Neil427/PEGASUS_2023_REVIVAL/Images/AamberPegasus6809.jpeg

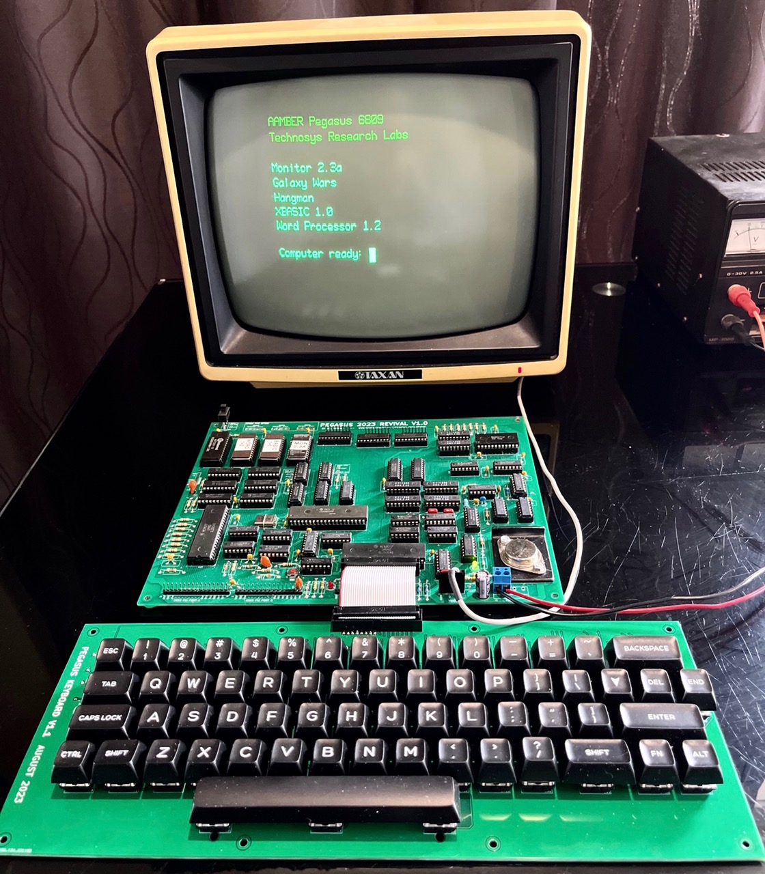
Images/AamberPegasus6809.jpeg
