Neil427/PEGASUS_2023_REVIVAL/Images/AamberPegasus6809b.jpeg

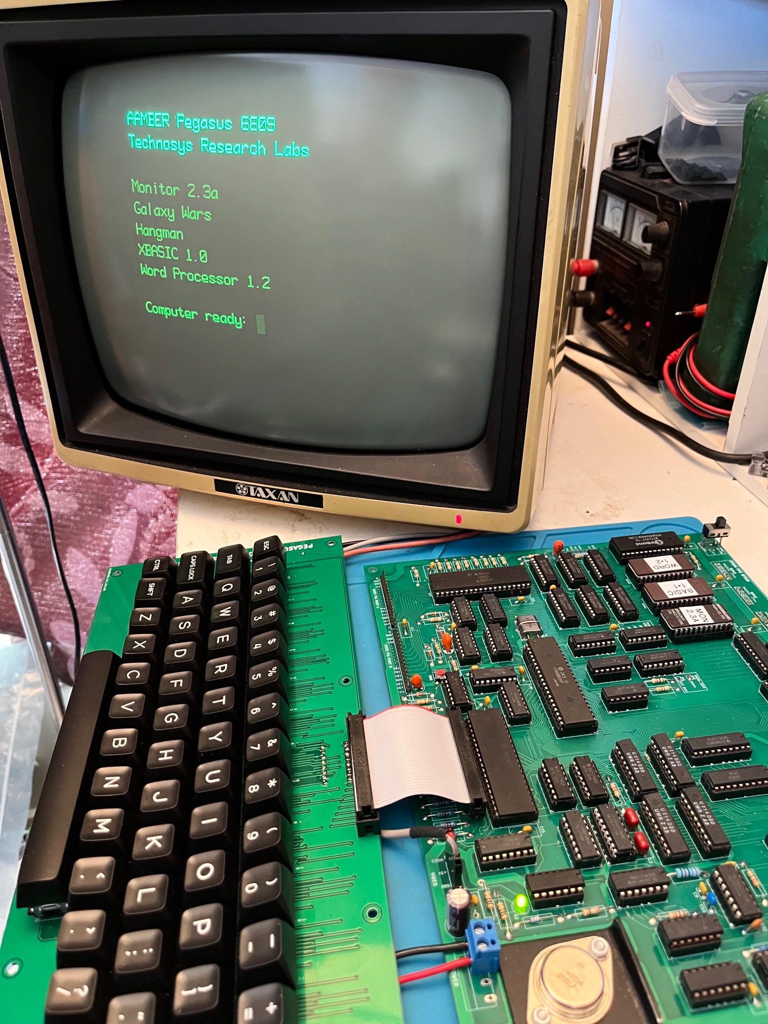
Images/AamberPegasus6809b.jpeg
