Neil427/PEGASUS_2023_REVIVAL/Images/OriginalPCBbottom.png

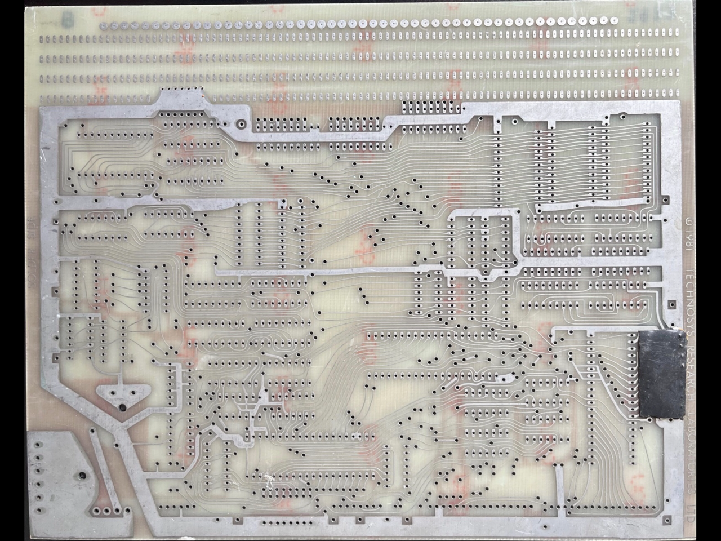
Images/OriginalPCBbottom.png
