Neil427/PEGASUS_2023_REVIVAL/Images/Pegasus The First Powerup.jpeg

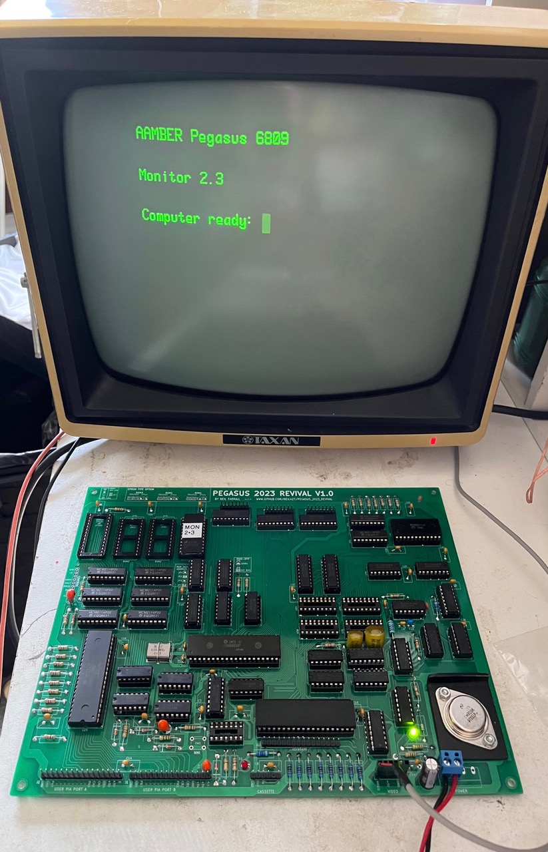
Images/Pegasus The First Powerup.jpeg
