Neil427/PEGASUS_2023_REVIVAL/Images/PegasusGalaxywars.jpeg

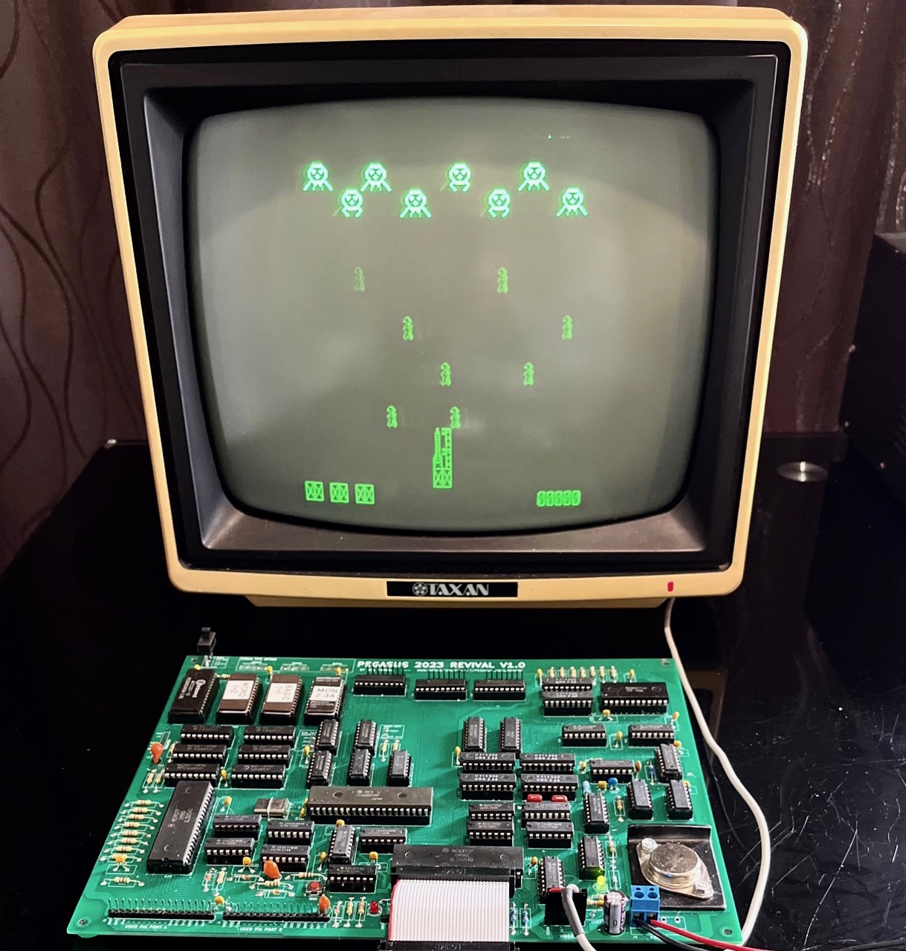
Images/PegasusGalaxywars.jpeg
