Neil427/PEGASUS_2023_REVIVAL/Images/PegasusHangman3.jpeg

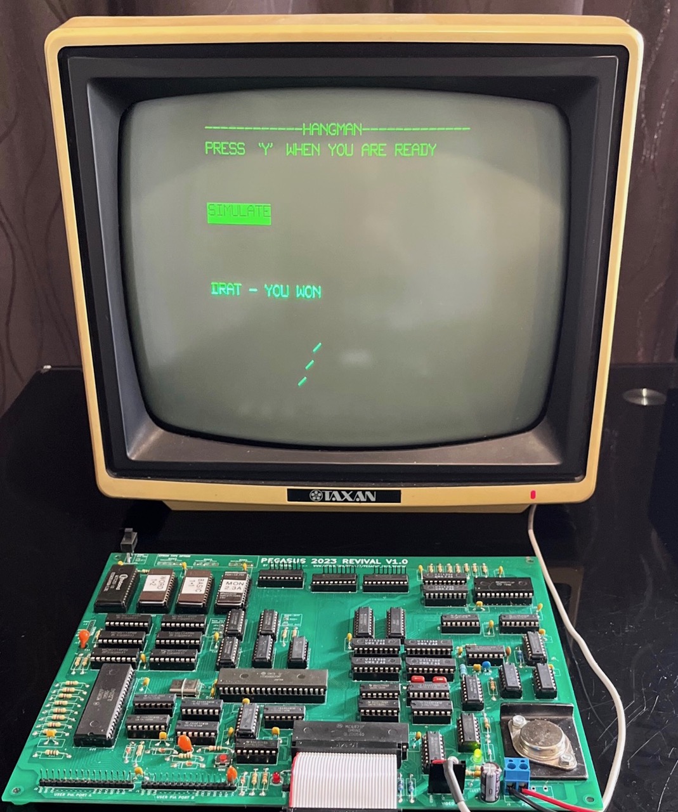
Images/PegasusHangman3.jpeg
