Neil427/PEGASUS_2023_REVIVAL/Images/PegasusHangman.jpeg

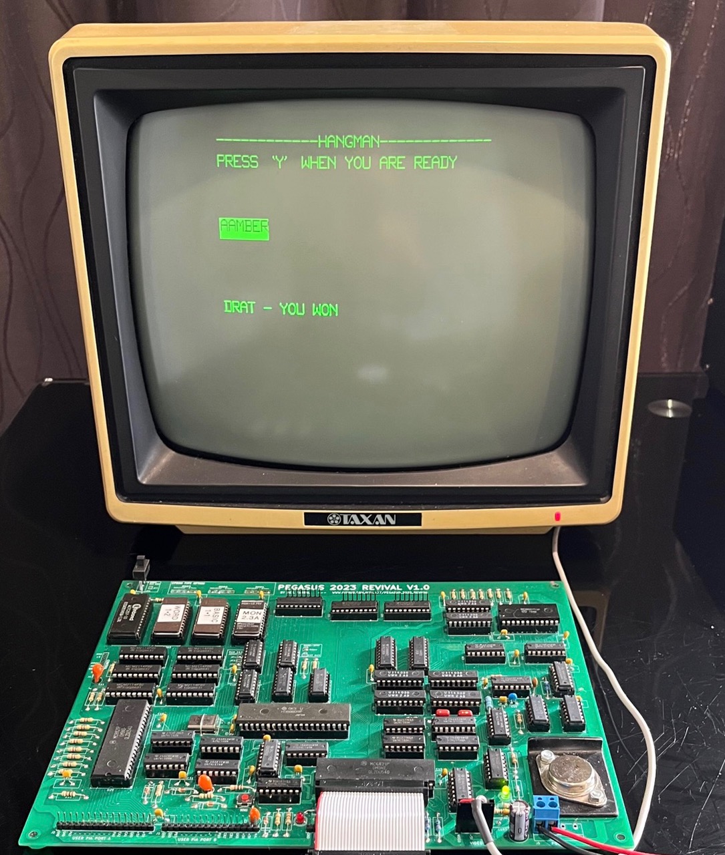
Images/PegasusHangman.jpeg
