Neil427/PEGASUS_2023_REVIVAL/Images/PegasusKeyboard.jpeg

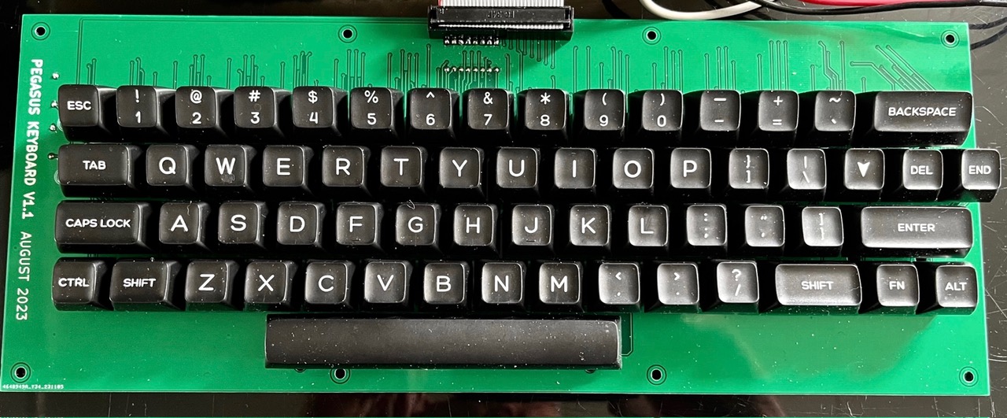
Images/PegasusKeyboard.jpeg
