Neil427/PEGASUS_2023_REVIVAL/Images/PegasusMainboard.jpeg

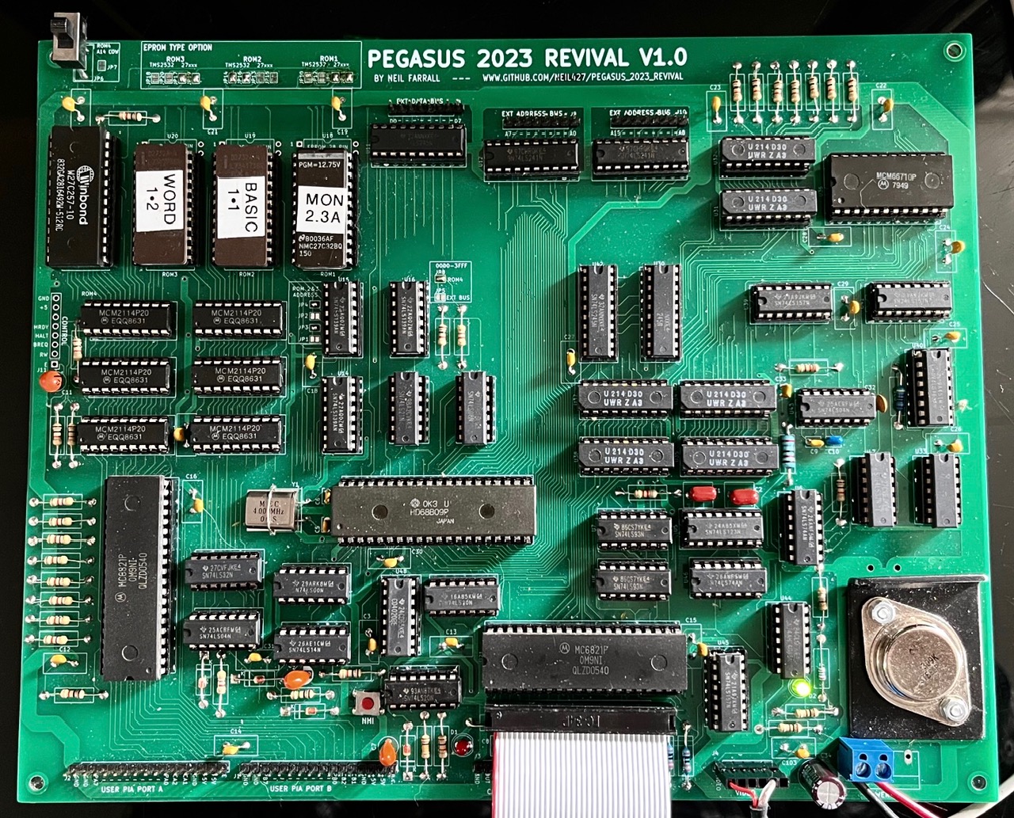
Images/PegasusMainboard.jpeg
