Neil427/PEGASUS_2023_REVIVAL/Keyboard_AamberPegasus2023Revival/Keyboard Keycaps.png

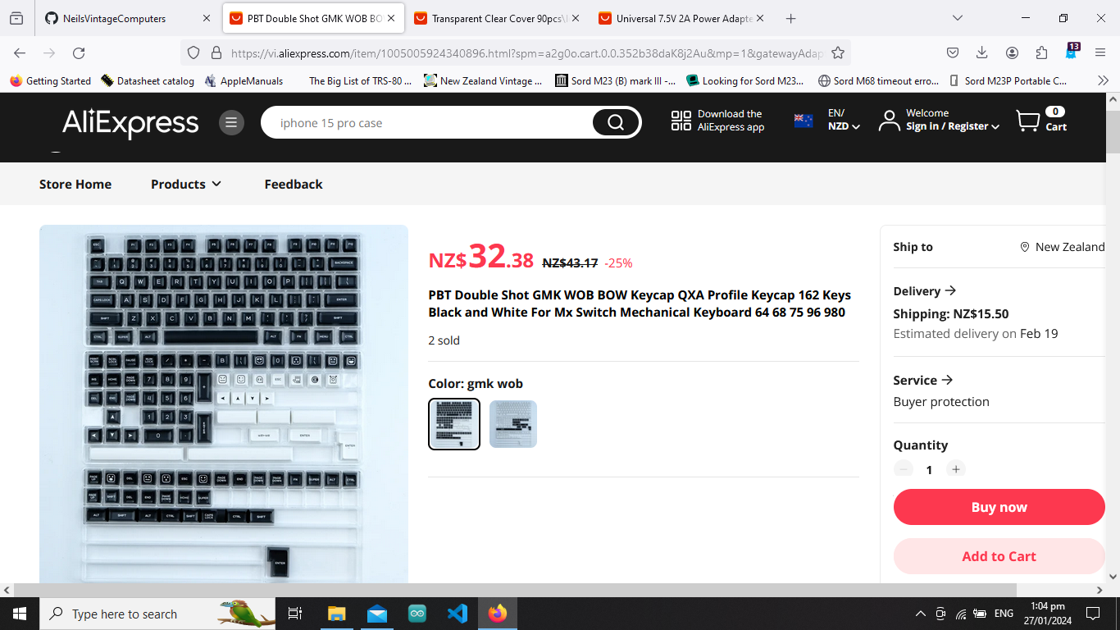
Keyboard_AamberPegasus2023Revival/Keyboard Keycaps.png
