Neil427/PEGASUS_2023_REVIVAL/Keyboard_AamberPegasus2023Revival/Keyboard Switches.png

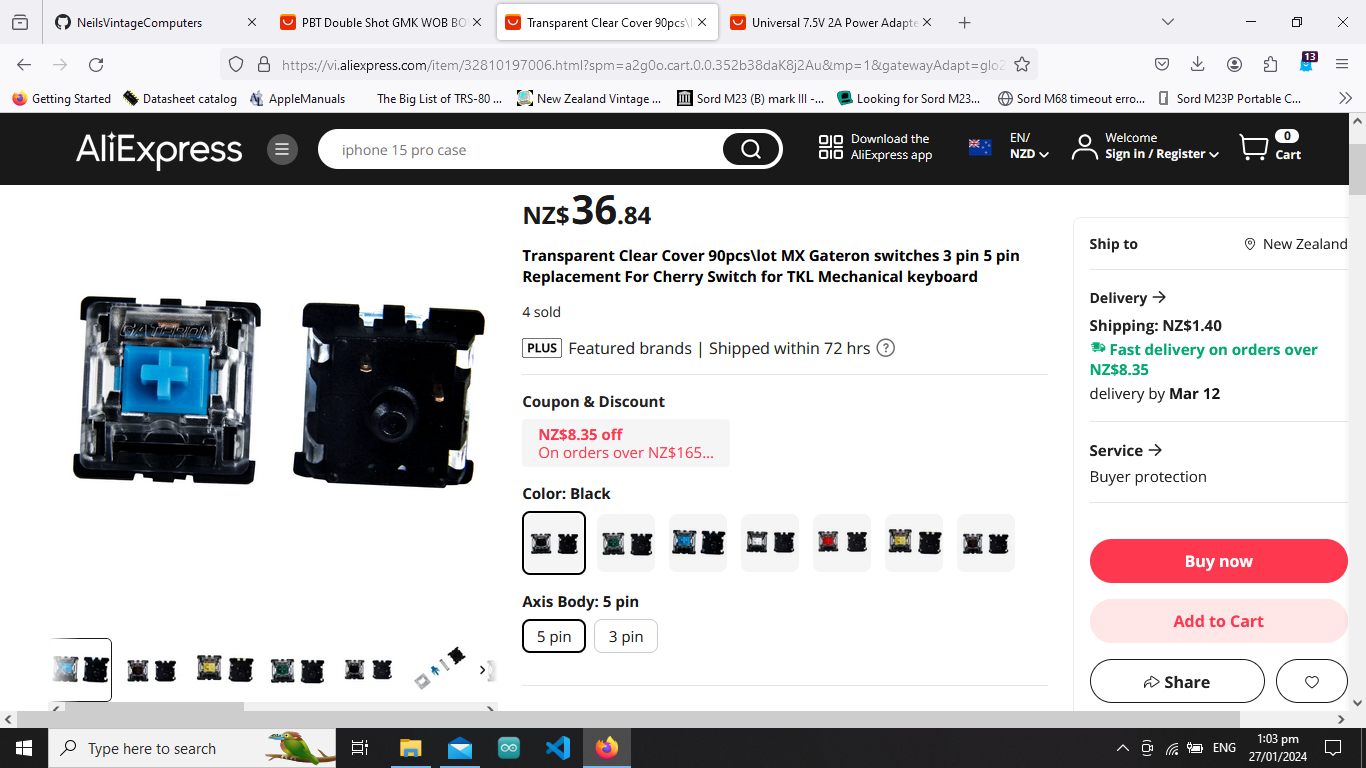
Keyboard_AamberPegasus2023Revival/Keyboard Switches.png
