Neil427/PEGASUS_2023_REVIVAL/Mainboard_AambePegasus2023Revival/Pegasus2023TOP3D.png

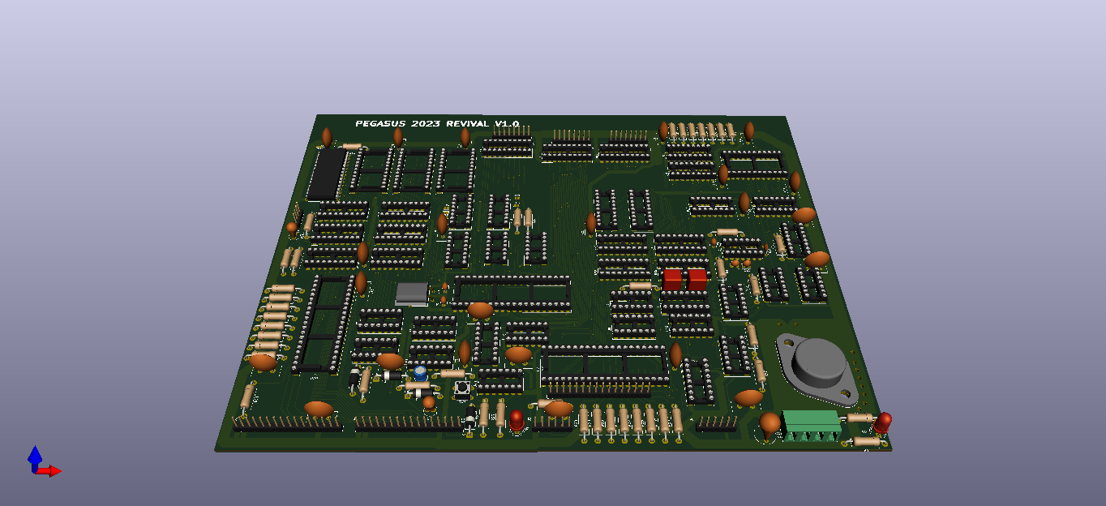
Mainboard_AambePegasus2023Revival/Pegasus2023TOP3D.png
