Neil427/PEGASUS_2023_REVIVAL/Mainboard_AambePegasus2023Revival/Plugpack.png

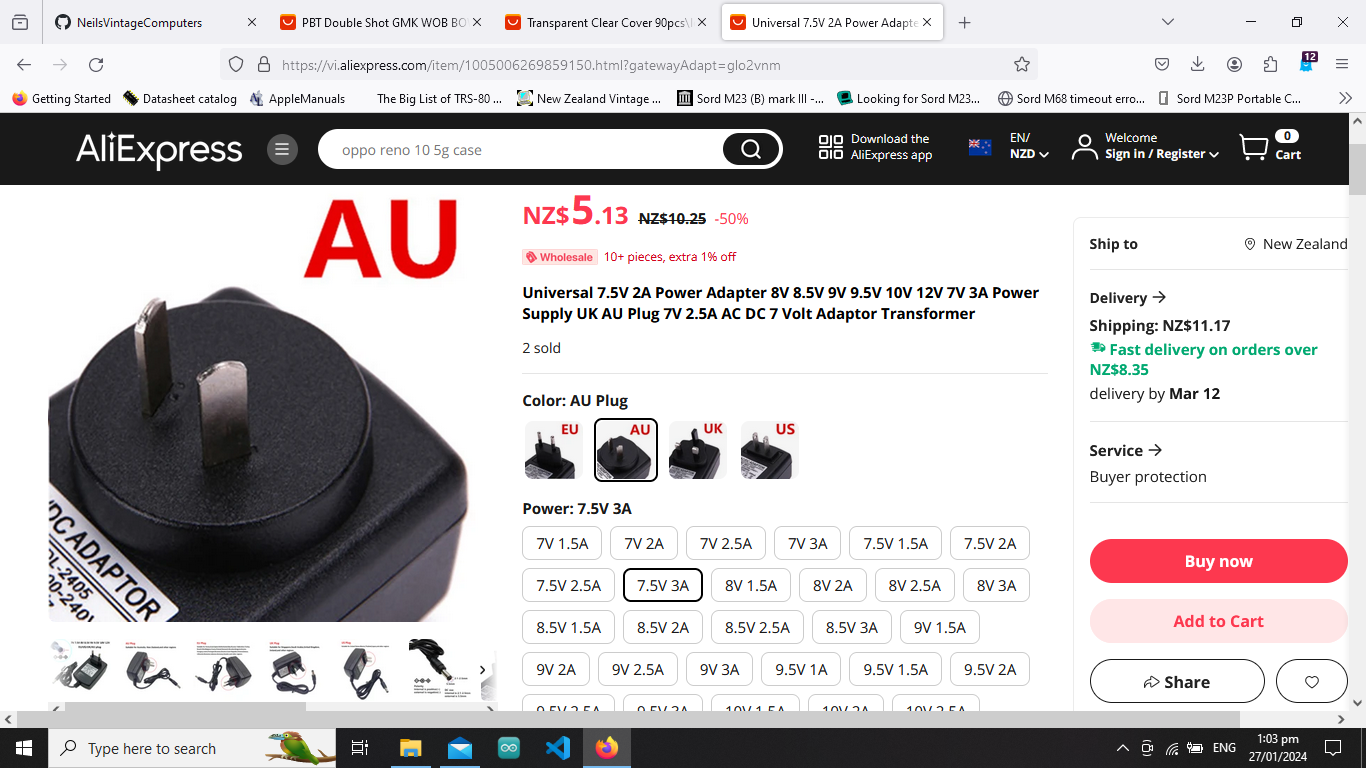
Mainboard_AambePegasus2023Revival/Plugpack.png
